Sphere-Corporation/ORB/pictures/WhatsApp Image 2024-01-04 at 21.14.18 (1).jpeg

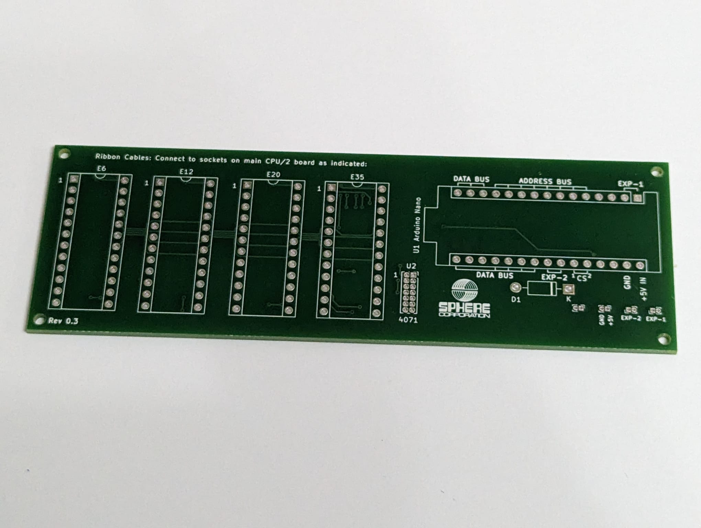
pictures/WhatsApp Image 2024-01-04 at 21.14.18 (1).jpeg
