Sphere-Corporation/ORB/source/orb/ORB-Test/pds-v3n.h

/// ROM image for : pds-v3n.bin
/// Date          : 23-MAY-2023
///
/// Created by convertROM v1.0
static const PROGMEM int ROM[] = {
142,1,255,48,223,38,223,12,134,31,183,240,65,206,15,255,
223,14,223,26,141,33,141,37,141,115,189,254,113,129,1,38,
3,189,253,161,129,5,38,2,141,61,129,18,38,2,141,63,
129,4,38,228,126,254,100,206,224,0,223,28,57,198,96,206,
226,0,9,231,0,156,28,38,249,57,222,28,99,0,206,38,
240,9,39,246,134,64,181,240,65,39,246,222,28,166,0,42,
2,99,0,182,240,64,57,222,12,223,32,222,14,223,34,141,
198,141,202,151,50,222,28,223,36,141,207,129,27,38,4,127,
0,50,57,141,10,32,242,129,13,45,172,46,18,134,96,129,
9,45,22,46,242,214,50,39,3,189,253,70,126,253,116,129,
18,45,40,46,8,222,28,32,31,141,103,32,64,129,20,45,
36,46,3,9,32,37,129,31,45,131,39,65,222,28,129,13,
39,4,167,0,129,96,39,76,8,32,16,222,28,198,32,9,
90,38,252,32,6,198,32,8,90,38,252,223,28,140,224,0,
44,4,141,177,141,50,140,226,0,43,24,141,23,214,50,39,
18,222,34,156,14,39,12,141,60,222,20,223,34,214,29,196,
224,215,29,57,214,50,39,10,222,32,223,22,222,36,141,38,
223,32,32,75,141,191,32,229,222,36,223,22,222,32,156,12,
39,35,9,156,12,39,8,9,230,0,193,96,38,245,8,223,
32,32,3,222,20,8,230,0,223,20,222,22,231,0,8,223,
22,193,96,38,238,57,206,225,224,95,55,230,0,8,193,96,
38,248,222,34,231,0,9,223,34,51,193,0,38,246,57,206,
224,0,230,32,231,0,8,140,225,224,38,246,223,28,223,22,
189,252,61,57,206,225,223,230,0,231,32,223,28,9,140,223,
255,38,244,198,96,8,231,0,140,224,31,38,248,57,222,17,
166,0,223,30,189,252,188,222,30,156,10,39,3,8,32,240,
57,127,0,4,222,32,223,64,222,38,223,2,166,8,230,7,
193,64,39,107,8,8,8,8,8,8,8,189,255,34,215,42,
151,43,222,2,166,0,230,1,222,64,223,44,193,61,38,6,
222,42,223,44,32,14,193,32,39,10,125,0,4,39,1,57,
215,4,32,192,141,65,150,44,167,0,150,45,167,1,222,2,
8,8,8,166,0,129,32,39,10,189,255,34,222,64,167,0,
8,223,64,222,2,166,6,222,64,129,69,46,49,39,33,129,
68,39,34,222,2,8,166,0,129,96,38,249,8,32,139,141,
6,238,0,223,42,32,155,72,95,151,1,215,0,222,0,57,
214,42,231,0,8,150,43,167,0,8,223,64,32,213,8,223,
64,150,43,144,65,9,167,0,32,201,48,230,5,166,6,128,
1,194,0,231,5,167,6,32,11,129,13,45,125,46,78,189,
252,203,49,49,141,118,141,9,189,252,165,222,64,141,9,32,
245,189,252,74,189,252,188,57,129,3,45,37,46,69,222,48,
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
};
