Sphere-Corporation/ORB/source/orb/ORB-Test/pinlayouts.h

constexpr int addressPin[]  = {9, 8, 7, 6, 5, 4, 3, 2};    // DIP switches connected to Address Lines D2-D9 

constexpr int dataPin[]  = {10, 11, 12, 13, A0, A1, A2, A3} ;// LED connections to Data Lines 

constexpr int chipSelectPin[]  = { A4, A5}; // Chip Select lines
